ldocull/Thetis_MIDI_UI/Arduino/TEST/MIDIenc.cpp

#include "MIDIenc.h"

// constructors
MIDIenc::MIDIenc(){};

MIDIenc::MIDIenc(int a, int b, byte num){
  myKnob = new Encoder(a, b);
	number = num;
  detentOrValue = 4; // CC changes once per detent
  value = 0;
  outLo = 0;
  outHi = 127;
};

MIDIenc::MIDIenc(int a, int b, byte num, byte detentOrValue){
  myKnob = new Encoder(a, b);
	number = num;
  this->detentOrValue = detentOrValue; // CC changes per encoder value or detent
  value = 0;
  outLo = 0;
  outHi = 127;
};

// destructor
MIDIenc::~MIDIenc(){
  delete myKnob;
};

int MIDIenc::sendRelative() {
  int oldValue = value;
  int newValue = readRelative();

  if (newValue != -1) {
    int difference = newValue - oldValue;

    int mappedChange = 0;

    if (difference > 0) {
      // Movement detected in the positive direction
      mappedChange = 1; // +1
    } else if (difference < 0) {
      // Movement detected in the negative direction
      mappedChange = -1; // -1
    }
    usbMIDI.sendControlChange(number, mappedChange, MIDIchannel);
    return mappedChange;
  }

  return -1; // If no new value was read, return -1
}

int MIDIenc::read(){
  int incdec = myKnob->read();

  if (incdec >= detentOrValue){
    myKnob->write(0);
    if ( value < outHi ){
      value++;
      return value;
    }
    else{ return -1; }
  }
  else if (incdec <= -detentOrValue){
    myKnob->write(0);
    if ( value > outLo ){
      value--;
      return value;
    }
    else{ return -1; }
  }
  else{ return -1; }
}


//
//  Returns +1/-1 with no end limits... WR9R
//
int MIDIenc::readRelative(){
  int incdec = myKnob->read();

  if (incdec >= detentOrValue){
    myKnob->write(0);
//    if ( value < outHi ){
      value++;
      return value;
//    }
//    else{ return -1; }
  }
  else if (incdec <= -detentOrValue){
    myKnob->write(0);
//    return value;
//    if ( value > outLo ){
      value--;
      return value;
//    }
//    else{ return -1; }
  }
  else{ return -1; }
}


int MIDIenc::send(){
  int newValue = read();
  if (newValue >= 0){
    value = newValue;
    if (number == PROGRAM_CHANGE){
      usbMIDI.sendProgramChange(value, MIDIchannel);
    }
    else{
      usbMIDI.sendControlChange(number, newValue, MIDIchannel);
    }
  }
  return newValue;
}

int MIDIenc::send(bool force){
  if (force){
    usbMIDI.sendControlChange(number, value, MIDIchannel);
    return value;
  }
  else{ return -1; }
}


// Manually set the value.
void MIDIenc::write(byte val){
  value = constrain(val, outLo, outHi);
};

// Set the CC number.
void MIDIenc::setControlNumber(byte num){
  number = num;
};

// Set upper and lower limits for outgoing MIDI messages.
void MIDIenc::outputRange(byte min, byte max){
  outLo = constrain(min, 0, 127);
  outHi = constrain(max, 0, 127);
};
